lessthan00/IMU/output/top-pcb.png

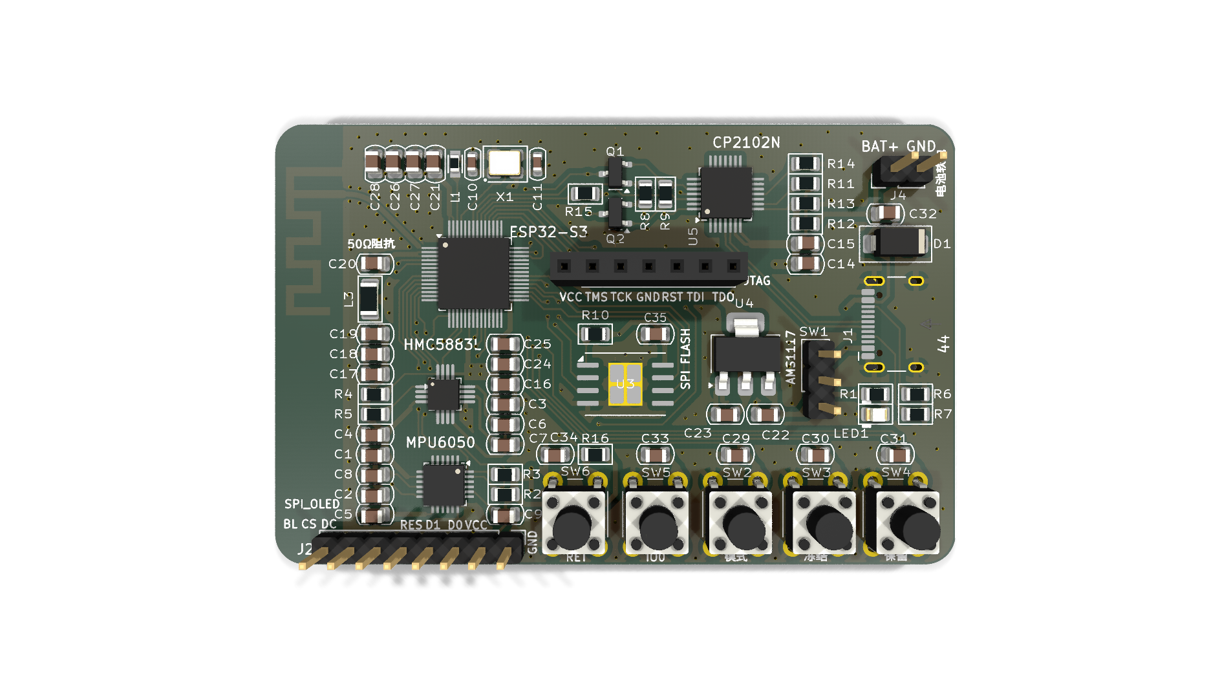
output/top-pcb.png
